prithvi-narayan-bhat/Custom_RISC_Implementation/rv32i_exTest.sv

/*
    Testing instructions with values where ever possible

    ________________________________________________________________________________________________
    |No. |SW pos |          Instruction Word             | Inst | rs1_data |    rs2      | output   |
    |-----------------------------------------------------------------------------------------------|
    |                       R Instruction                                                           |
    |-----------------------------------------------------------------------------------------------|
    | 0  | 00000 | 0000000 00000 00000 000 00000 0110011 | ADD  | h2000000  | h30000000  | 32000000 |
    | 1  | 00001 | 0100000 00000 00000 000 00000 0110011 | SUB  | d3        | d2         | 00000001 |
    | 2  | 00010 | 0000000 00000 00000 001 00000 0110011 | SLL  | h2000000  | h00000002  | 08000000 |
    | 3  | 00011 | 0000000 00000 00000 010 00000 0110011 | SLT  | d3        | d2         | 00000000 |
    | 4  | 00100 | 0000000 00000 00000 011 00000 0110011 | SLTU | h2000000  | h30000000  | 00000001 |
    | 5  | 00101 | 0000000 00000 00000 100 00000 0110011 | XOR  | d3        | d2         | 00000001 |
    | 6  | 00110 | 0000000 00000 00000 101 00000 0110011 | SRL  | d3        | d2         | 00000000 |
    | 7  | 00111 | 0100000 00000 00000 101 00000 0110011 | SRA  | d3        | d2         | 00000000 |
    | 8  | 01000 | 0000000 00000 00000 110 00000 0110011 | OR   | d3        | d2         | 00000003 |
    | 9  | 01001 | 0000000 00000 00000 111 00000 0110011 | AND  | d3        | d2         | 00000002 |
    |_______________________________________________________________________________________________|
    |                       I Instructions                                                          |
    |-----------------------------------------------------------------------------------------------|
    | 10 | 01010 | 000000000010 00000 000 00000 1100111  | JALR | d3        | DC         | 00000005 |
    | 11 | 01011 | 000000000010 00000 000 00000 0000011  | LB   | d3        | DC         | 00000005 |
    | 12 | 01100 | 000000000010 00000 001 00000 0000011  | LH   | d3        | DC         | 00000005 |
    | 13 | 01101 | 000000000010 00000 010 00000 0000011  | LW   | d3        | DC         | 00000005 |
    | 14 | 01110 | 000000000010 00000 100 00000 0000011  | LBU  | d3        | DC         | 00000005 |
    | 15 | 01111 | 000000000010 00000 101 00000 0000011  | LHU  | d3        | DC         | 00000005 |
    | 16 | 10000 | 000000000010 00000 000 00000 0010011  | ADDI | h2000000  | h456       | 02000456 |
    | 17 | 10001 | 000000000010 00000 010 00000 0010011  | SLTI | d3        | DC         | 00000000 |
    | 18 | 10010 | 000000000010 00000 011 00000 0010011  | SLTIU| d3        | DC         | 00000000 |
    | 19 | 10011 | 000000000010 00000 100 00000 0010011  | XORI | d3        | DC         | 00000001 |
    | 20 | 10100 | 000000000010 00000 110 00000 0010011  | ORI  | d3        | DC         | 00000003 |
    | 21 | 10101 | 000000000010 00000 111 00000 0010011  | ANDI | d3        | DC         | 00000002 |
    | 22 | 10110 | 000000000010 00000 001 00000 0010011  | SLLI | d3        | DC         | 0000000C |
    | 23 | 10111 | 000000000010 00000 101 00000 0010011  | SRLI | d3        | DC         | 00000000 |
    | 24 | 11000 | 000000000010 00000 101 00000 0010011  | SRAI | d3        | DC         | 00000000 |
    |-----------------------------------------------------------------------------------------------|
    |                       U Instructions                                                          |
    |-----------------------------------------------------------------------------------------------|
    | 25 | 11001 | 00000000000000000000 00000 0110111    | LUI  | DC        | DC         | 12345000 |
    | 26 | 11010 | 00000000000000000000 00000 0010111    | AUIPC| DC        | DC         | 00000001 |
    |-----------------------------------------------------------------------------------------------|
    |                       J Instructions                                                          |
    |-----------------------------------------------------------------------------------------------|
    | 27 | 11011 | 00000000000000000000 00000 1101111    | JAL  | h12345678 | DC         | 1234567C |
    |-----------------------------------------------------------------------------------------------|
    |                       S Instructions                                                          |
    |-----------------------------------------------------------------------------------------------|
    | 28 | 11100 | 0100010 00000 00000 000 10110 0100011 |  SB  | h2000000  | DC         | 02000456 |
    | 29 | 11101 | 0100010 00000 00000 001 00000 0100011 |  SH  | d3        | 00000005   | 02000456 |
    | 30 | 11110 | 0100010 00000 00000 010 00000 0100011 |  SW  | d3        | 00000005   | 02000456 |
    |-----------------------------------------------------------------------------------------------|

*/
module rv32i_exTest(
        input clk,
        input [1:0] KEY,
        input [9:0] SW
    );

    wire [4:0] operation = SW[4:0];
    wire [31:0] iw_out;
    wire [31:0] rs1_data_out, rs2_data_out, pc_out;

    // Set instruction word based on switch position
    always @ (SW) begin
        case (operation)
            /*---------------------------------------------------------Register---------------------------------------------------------*/
            5'b00000:
            begin
                iw_out = 32'b00000000000000000000000000110011;          // ADD  => 32000000
                rs1_data_out = 32'h2000000;
                rs2_data_out = 32'h30000000;
            end

            5'b00001:
            begin
                iw_out = 32'b01000000000000000000000000110011;          // SUB  => 00000001
                rs1_data_out = 32'd3;
                rs2_data_out = 32'd2;
            end

            5'b00010:
            begin
                iw_out = 32'b00000000000000000001000000110011;          // SLL  => 08000000
                rs1_data_out = 32'h2000000;
                rs2_data_out = 32'h00000002;
            end

            5'b00011:
            begin
                iw_out = 32'b00000000000000000010000000110011;          // SLT  => 00000000
                rs1_data_out = 32'd3;
                rs2_data_out = 32'd2;
            end

            5'b00100:
            begin
                iw_out = 32'b00000000000000000011000000110011;          // SLTU => 00000001
                rs1_data_out = 32'h2000000;
                rs2_data_out = 32'h30000000;
            end

            5'b11111:
            begin
                iw_out = 32'b00000000000000000011000000110011;          // SLTU => 00000001
                rs1_data_out = 32'h2000000;
                rs2_data_out = 32'h20000000;
            end

            5'b00101:
            begin
                iw_out = 32'b00000000000000000100000000110011;          // XOR  => 00000001
                rs1_data_out = 32'd3;
                rs2_data_out = 32'd2;
            end

            5'b00110:
            begin
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
                rs2_data_out = 32'd2;
            end

            5'b11000:
            begin
                iw_out = 32'b01000000001000000101000000010011;    // SRAI => 00000000
                rs1_data_out = 32'd3;
                rs2_data_out = 32'd2;
            end

            5'b11001:
            begin
                iw_out = 32'b00010010001101000101000000110111;    // LUI  => 00012345
                rs1_data_out = 32'd3;
                rs2_data_out = 32'd2;
            end

            5'b11010:
            begin
                iw_out = 32'b00000000000000000000000000010111;    // AUIPC=> 00000001
                rs1_data_out = 32'd3;
                rs2_data_out = 32'd2;
                pc_out = 32'd1;
            end

            5'b11011:
            begin
                iw_out = 32'b00000000000000000000000001101111;          // JAL => 1234567C
                pc_out = 32'h12345678;
            end

            5'b11100:
            begin
                iw_out = 32'b01000100000000000000101100100011;          // SB   => 02000456
                rs1_data_out = 32'h2000000;
            end

            5'b11101:
            begin
                iw_out = 32'b01000100000000000000101100100011;    // SH   => 00000005
                rs1_data_out = 32'd3;
            end

            5'b11110:
            begin
                iw_out = 32'b01000100000000000000101100100011;    // SW   => 00000005
                rs1_data_out = 32'd3;
            end


            default:  iw_out = 32'b0;
        endcase
    end

   // rv32i_exTop test (.clk(ADC_CLK_10), .reset(0), .pc_in(pc_out), .iw_in(iw_out), .rs1_data_in(rs1_data_out), .rs2_data_in(rs2_data_out));      // Instantiate module
endmodule
